sKribble45/GlucoView/firmware/src/glucose/bg_datasource.h

#include <Arduino.h>
#include "config/config_manager.h"

#ifndef __BG_DATASOURCE_H
#define __BG_DATASOURCE_H
typedef enum{
    DEXCOM,
    NIGHTSCOUT
} BGDataSource;

typedef struct {
    int minsSinceReading;
    unsigned long timestamp;
    unsigned long tztimestamp;
    double bg;
    double delta;
    int mgdl;
    int mgdlDelta;
    char trendDescription[14];

    bool failed;
} GlucoseReading;

extern GlucoseReading dsGl;
extern Config bgDSConfig;

double MgdlToMmol(int mgdl);
void UpdateDataSourceConfig(Config config);
bool BgDataSourceInit();
bool GetGl();
GlucoseReading GlNow();
void PrintGlucose(GlucoseReading gl);

#endif
