sKribble45/GlucoView/firmware/src/update_manager.h

#include "config\config_manager.h"

#ifndef __UPDATE_MANAGER_H
#define __UPDATE_MANAGER_H

bool CheckForUpdate();
bool UpdateFromUrl(String url);
String GetFirmwareUrl();
extern RTC_DATA_ATTR bool updateNeeded;
extern RTC_DATA_ATTR time_t lastCheckedForUpdates;
extern Config updateConfig;
void UpdateUpdateManagerConfig(Config config);
void UpdateMode();
void OtaUpdate();

typedef struct{
    int major;
    int minor;
    int revision;
    int build;
} Version;

#endif
